CCMEELBOOM/DSIM_Work/CODE/Image_Gallery/PXL_20260513_221533852~2.jpg

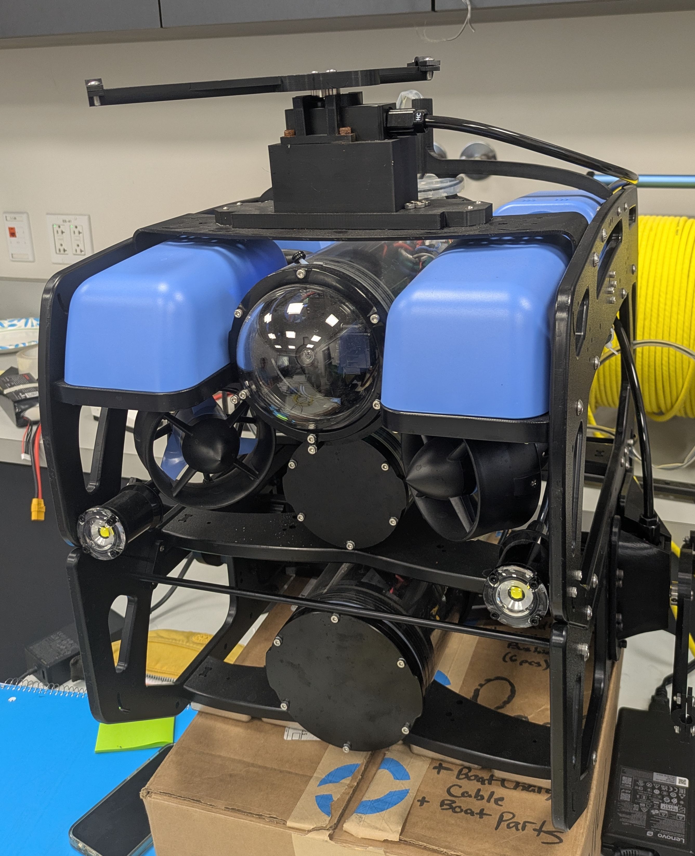
CODE/Image_Gallery/PXL_20260513_221533852~2.jpg
