CCMEELBOOM/DSIM_Work/CODE/Image_Gallery/PXL_20260513_221630130.jpg

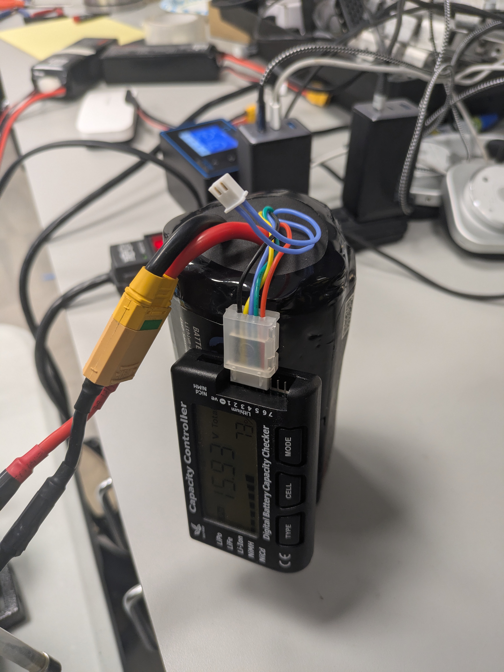
CODE/Image_Gallery/PXL_20260513_221630130.jpg
