CCMEELBOOM/DSIM_Work/CODE/Image_Gallery/PXL_20260513_221637603.jpg

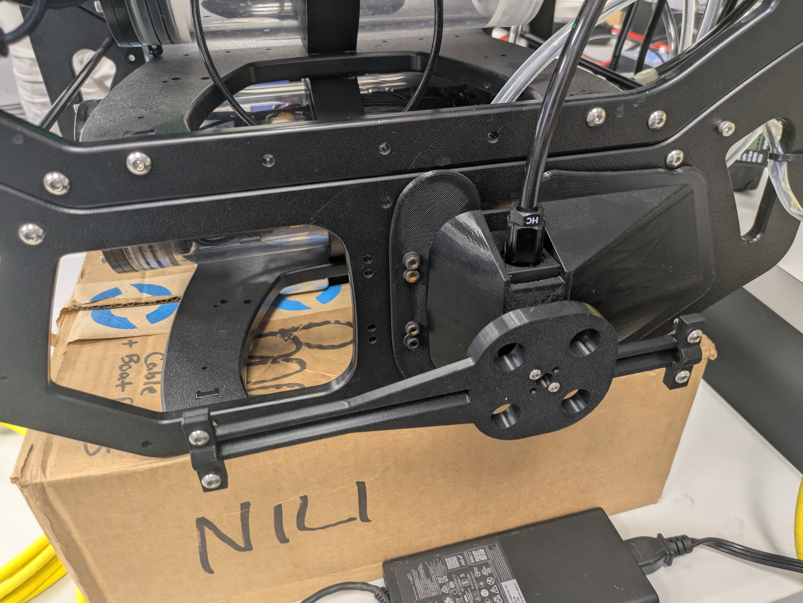
CODE/Image_Gallery/PXL_20260513_221637603.jpg
