CCMEELBOOM/DSIM_Work/CODE/Image_Gallery/PXL_20260513_221649425.jpg

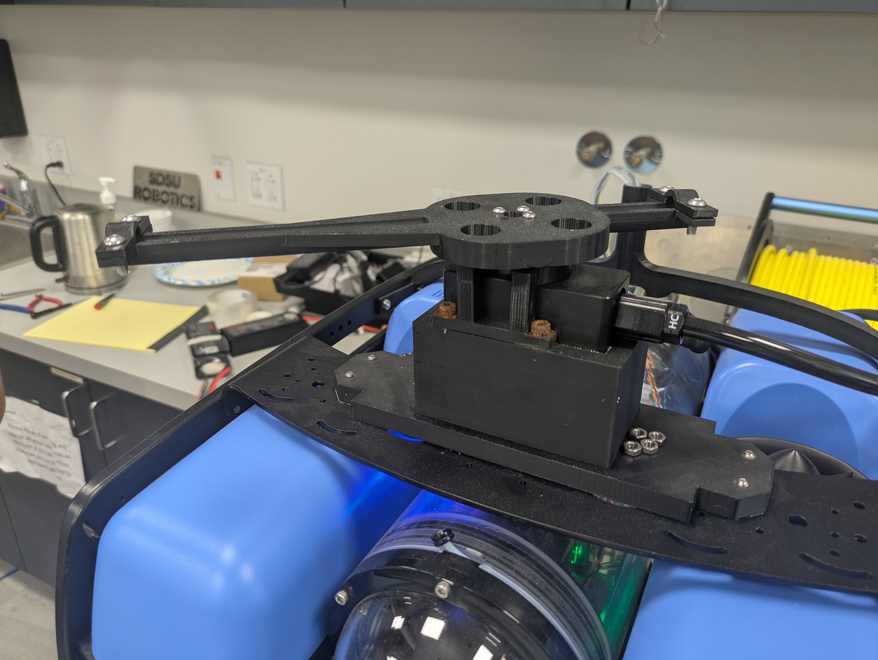
CODE/Image_Gallery/PXL_20260513_221649425.jpg
