CCMEELBOOM/DSIM_Work/CODE/Image_Gallery/PXL_20260513_221702240.jpg

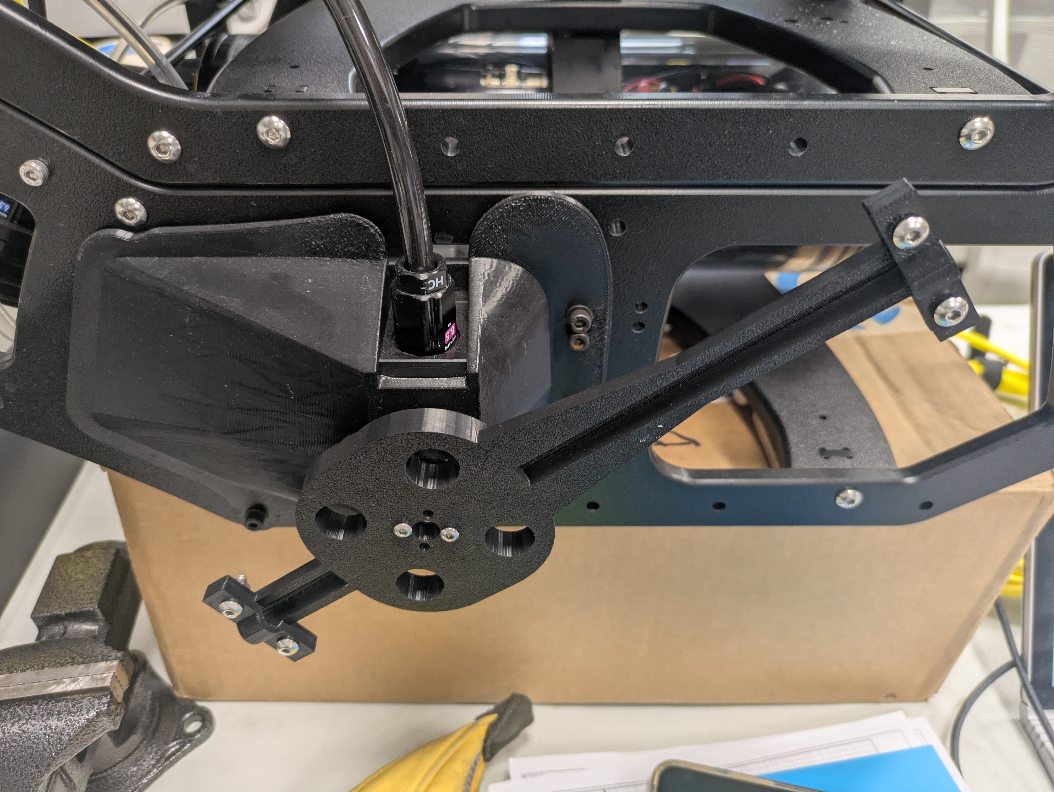
CODE/Image_Gallery/PXL_20260513_221702240.jpg
