CCMEELBOOM/DSIM_Work/CODE/Image_Gallery/PXL_20260519_230056400.jpg

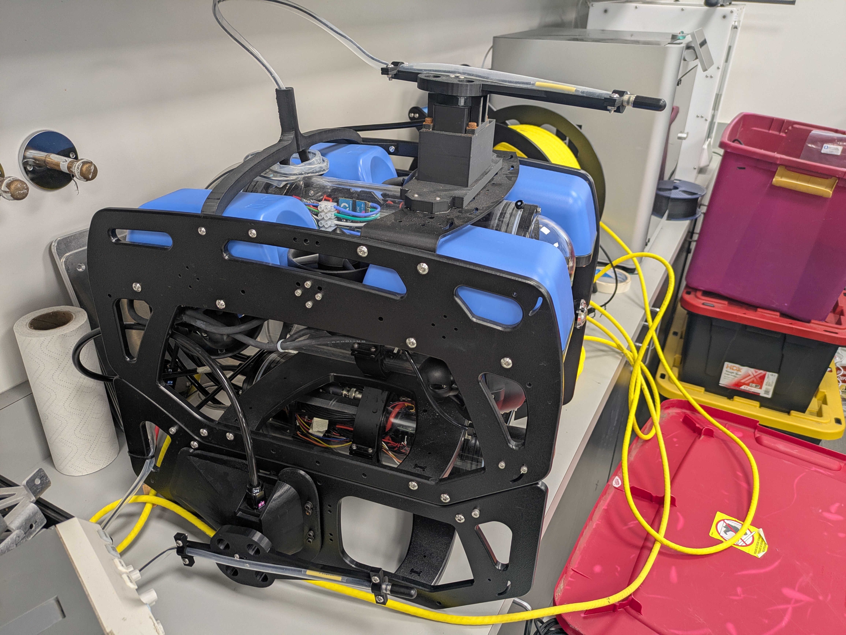
CODE/Image_Gallery/PXL_20260519_230056400.jpg
