CCMEELBOOM/DSIM_Work/CODE/Image_Gallery/PXL_20260519_230122678.jpg

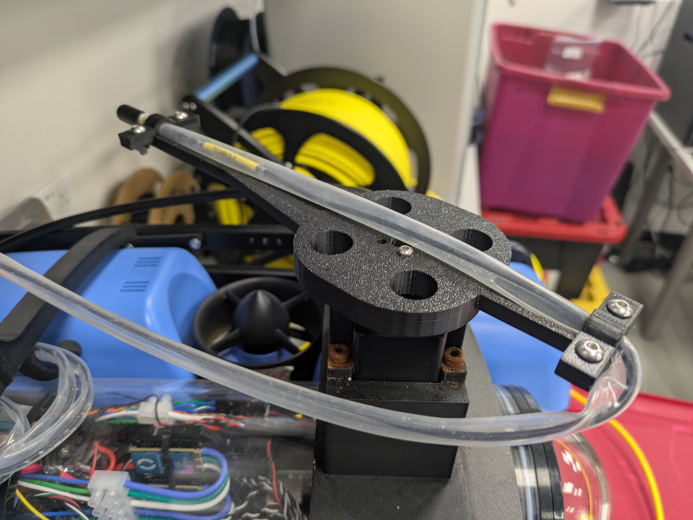
CODE/Image_Gallery/PXL_20260519_230122678.jpg
