CCMEELBOOM/DSIM_Work/CODE/Image_Gallery/Screenshot 2026-05-19 at 2.18.45 PM.png

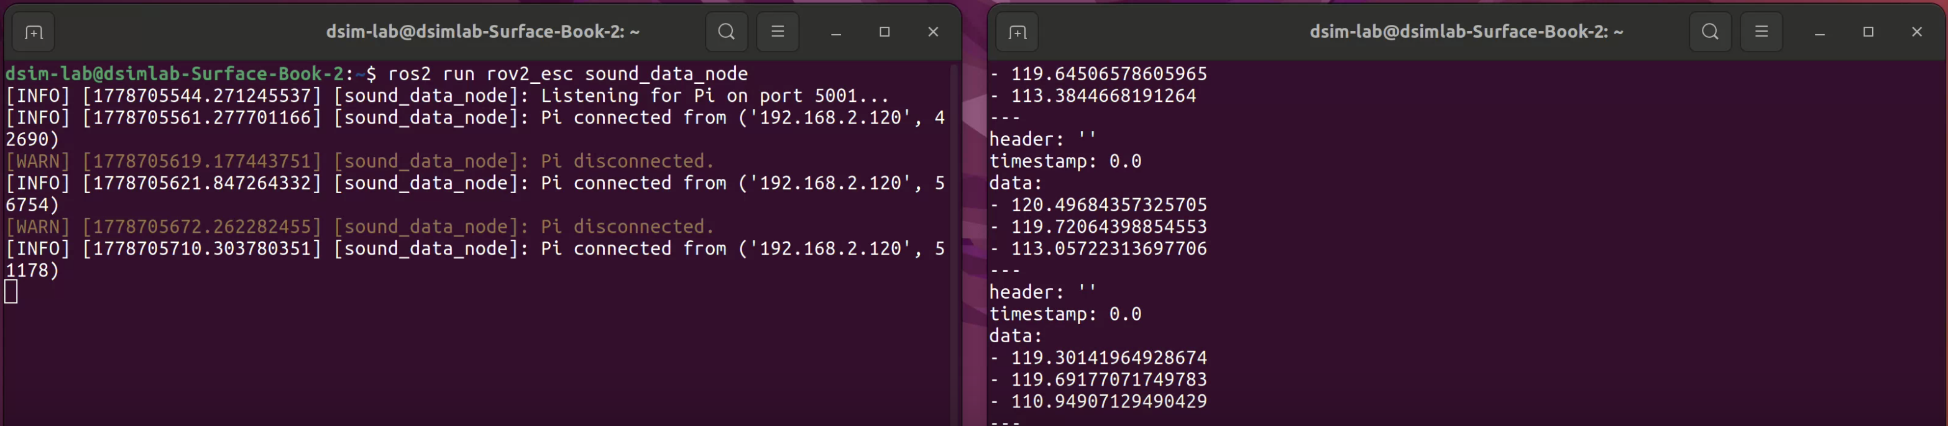
CODE/Image_Gallery/Screenshot 2026-05-19 at 2.18.45 PM.png
