CCMEELBOOM/DSIM_Work/Documentation/CAD/DSIM_BlueRov_with_attachments_isotropic (1).png

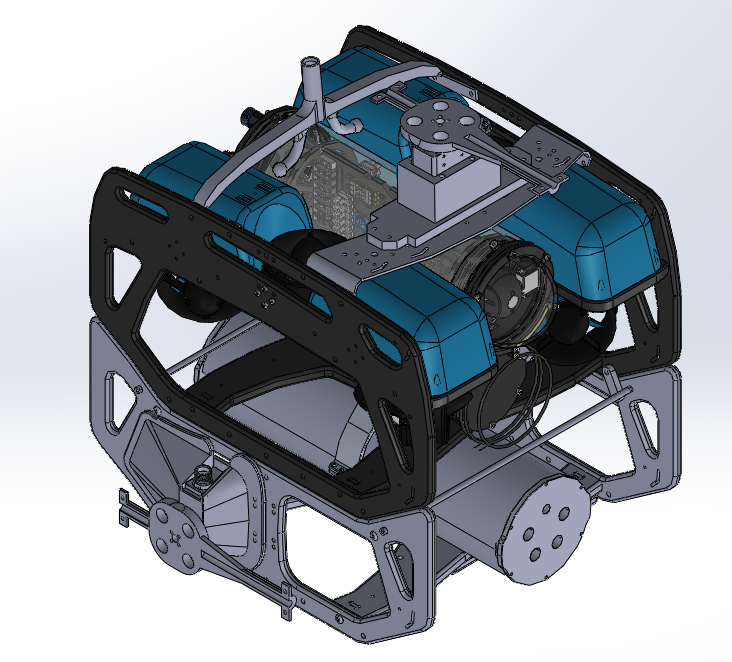
Documentation/CAD/DSIM_BlueRov_with_attachments_isotropic (1).png
