CCMEELBOOM/DSIM_Work/Documentation/CAD/DSIM_BlueRov_with_attachments_rear.png

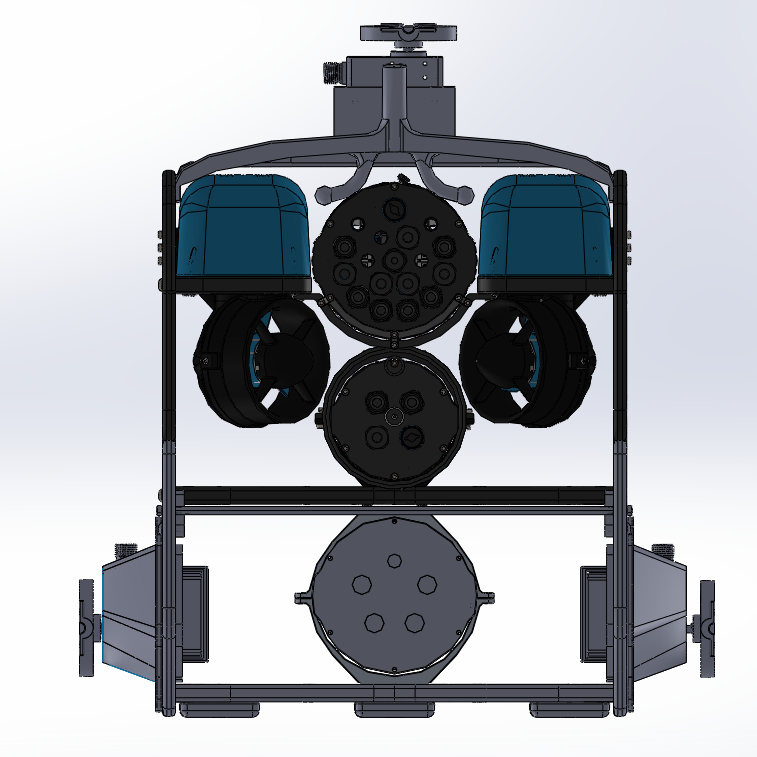
Documentation/CAD/DSIM_BlueRov_with_attachments_rear.png
