CCMEELBOOM/DSIM_Work/Documentation/Website.png

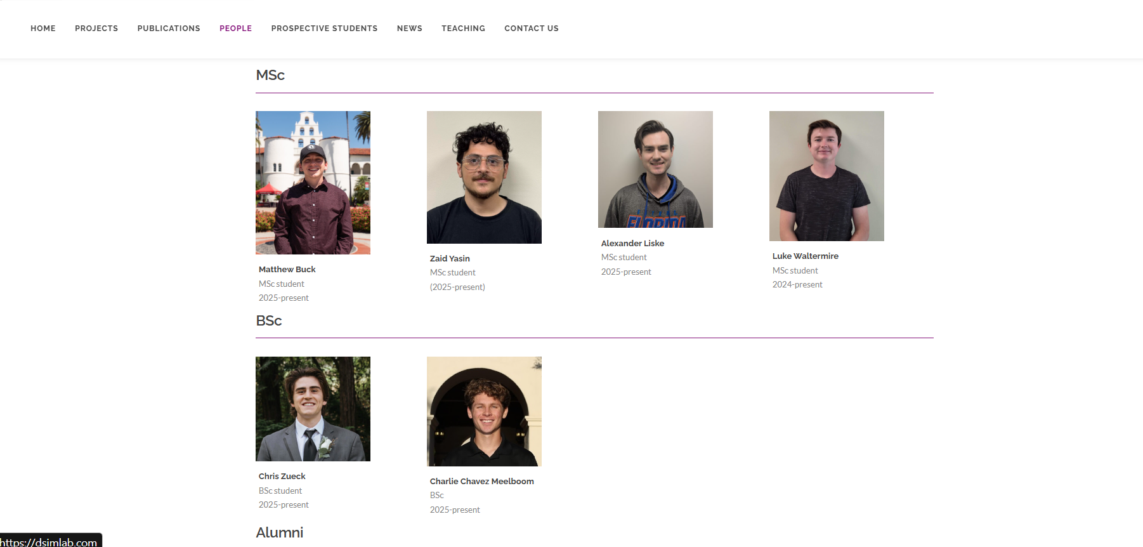
Documentation/Website.png
